tinyfpga/TinyFPGA-B-Series/bootloader/verilog/usb_fs_pe.v

module usb_fs_pe #(
  NUM_OUT_EPS = 1,
  NUM_IN_EPS = 1
) (
  input clk,
  input [6:0] dev_addr,


  ////////////////////////////////////////////////////////////////////////////////
  ////////////////////////////////////////////////////////////////////////////////
  /// USB Endpoint Interface
  ////////////////////////////////////////////////////////////////////////////////
  ////////////////////////////////////////////////////////////////////////////////

  ////////////////////
  // global endpoint interface 
  ////////////////////
  output reset,


  ////////////////////
  // out endpoint interfaces 
  ////////////////////
  input [NUM_OUT_EPS-1:0] out_ep_req,
  output [NUM_OUT_EPS-1:0] out_ep_grant,
  output [NUM_OUT_EPS-1:0] out_ep_data_avail,
  output [NUM_OUT_EPS-1:0] out_ep_setup,
  input [NUM_OUT_EPS-1:0] out_ep_data_get,
  output [7:0] out_ep_data,
  input [NUM_OUT_EPS-1:0] out_ep_stall,
  output [NUM_OUT_EPS-1:0] out_ep_acked,


  ////////////////////
  // in endpoint interfaces 
  ////////////////////
  input [NUM_IN_EPS-1:0] in_ep_req,
  output [NUM_IN_EPS-1:0] in_ep_grant,
  output [NUM_IN_EPS-1:0] in_ep_data_free,
  input [NUM_IN_EPS-1:0] in_ep_data_put,
  input [(NUM_IN_EPS*8)-1:0] in_ep_data,
  input [NUM_IN_EPS-1:0] in_ep_data_done,
  input [NUM_IN_EPS-1:0] in_ep_stall,
  output [NUM_IN_EPS-1:0] in_ep_acked,

  
  ////////////////////
  // sof interface
  ////////////////////
  output sof_valid,
  output [10:0] frame_index,



  ////////////////////////////////////////////////////////////////////////////////
  ////////////////////////////////////////////////////////////////////////////////
  /// USB TX/RX Interface
  ////////////////////////////////////////////////////////////////////////////////
  ////////////////////////////////////////////////////////////////////////////////

  inout dp,
  inout dn
);
  // in pe interface
  wire [7:0] arb_in_ep_data;

  // rx interface
  wire bit_strobe;
  wire rx_pkt_start;
  wire rx_pkt_end;
  wire [3:0] rx_pid;
  wire [6:0] rx_addr;
  wire [3:0] rx_endp;
  wire [10:0] rx_frame_num;
  wire rx_data_put;
  wire [7:0] rx_data;
  wire rx_pkt_valid;

  // tx mux
  wire in_tx_pkt_start;
  wire [3:0] in_tx_pid;
  wire out_tx_pkt_start;
  wire [3:0] out_tx_pid;
  
  // tx interface
  wire tx_pkt_start;
  wire tx_pkt_end;
  wire [3:0] tx_pid;
  wire tx_data_avail;
  wire tx_data_get;
  wire [7:0] tx_data;

  // sof interface
  assign sof_valid = rx_pkt_end && rx_pkt_valid && rx_pid == 4'b0101;
  assign frame_index = rx_frame_num;

  // d+/d- muxing and interface
  wire usb_output_enable;
  wire dp_tx;
  wire dn_tx;
  wire dp_rx;
  wire dn_rx;

  wire reset_i;
  assign reset = reset_i;


  usb_fs_in_arb #(
    .NUM_IN_EPS(NUM_IN_EPS)
  ) usb_fs_in_arb_inst (
    // endpoint interface 
    .in_ep_req(in_ep_req),
    .in_ep_grant(in_ep_grant),
    .in_ep_data(in_ep_data),

    // protocol engine interface 
    .arb_in_ep_data(arb_in_ep_data)
  );

  usb_fs_out_arb #(
    .NUM_OUT_EPS(NUM_OUT_EPS)
  ) usb_fs_out_arb_inst (
    // endpoint interface 
    .out_ep_req(out_ep_req),
    .out_ep_grant(out_ep_grant)
  );

  usb_fs_in_pe #(
    .NUM_IN_EPS(NUM_IN_EPS)
  ) usb_fs_in_pe_inst (
    .clk(clk),
    .reset(reset_i),
    .dev_addr(dev_addr),

    // endpoint interface 
    .in_ep_data_free(in_ep_data_free),
    .in_ep_data_put(in_ep_data_put),
    .in_ep_data(arb_in_ep_data),
    .in_ep_data_done(in_ep_data_done),
    .in_ep_stall(in_ep_stall),
    .in_ep_acked(in_ep_acked),

    // rx path 
    .rx_pkt_start(rx_pkt_start),
    .rx_pkt_end(rx_pkt_end),
    .rx_pkt_valid(rx_pkt_valid),
    .rx_pid(rx_pid),
    .rx_addr(rx_addr),
    .rx_endp(rx_endp),
    .rx_frame_num(rx_frame_num),

    // tx path 
    .tx_pkt_start(in_tx_pkt_start),
    .tx_pkt_end(tx_pkt_end),
    .tx_pid(in_tx_pid),
    .tx_data_avail(tx_data_avail),
    .tx_data_get(tx_data_get),
    .tx_data(tx_data)
  );

  usb_fs_out_pe #(
    .NUM_OUT_EPS(NUM_OUT_EPS)
  ) usb_fs_out_pe_inst (
    .clk(clk),
    .reset(reset_i),
    .dev_addr(dev_addr),

    // endpoint interface 
    .out_ep_data_avail(out_ep_data_avail),
    .out_ep_data_get(out_ep_data_get),
    .out_ep_data(out_ep_data),
    .out_ep_setup(out_ep_setup),
    .out_ep_stall(out_ep_stall),
    .out_ep_acked(out_ep_acked),

    // rx path 
    .rx_pkt_start(rx_pkt_start),
    .rx_pkt_end(rx_pkt_end),
    .rx_pkt_valid(rx_pkt_valid),
    .rx_pid(rx_pid),
    .rx_addr(rx_addr),
    .rx_endp(rx_endp),
    .rx_frame_num(rx_frame_num),
    .rx_data_put(rx_data_put),
    .rx_data(rx_data),

    // tx path 
    .tx_pkt_start(out_tx_pkt_start),
    .tx_pkt_end(tx_pkt_end),
    .tx_pid(out_tx_pid)
  );

  usb_fs_rx usb_fs_rx_inst (
    .clk_48mhz(clk),
    .reset(reset_i),
    .dp(dp_rx),
    .dn(dn_rx),
    .bit_strobe(bit_strobe),
    .pkt_start(rx_pkt_start),
    .pkt_end(rx_pkt_end),
    .pid(rx_pid),
    .addr(rx_addr),
    .endp(rx_endp),
    .frame_num(rx_frame_num),
    .rx_data_put(rx_data_put),
    .rx_data(rx_data),
    .valid_packet(rx_pkt_valid)
  );

  usb_fs_tx_mux usb_fs_tx_mux_inst (
    // interface to IN Protocol Engine
    .in_tx_pkt_start(in_tx_pkt_start),
    .in_tx_pid(in_tx_pid),

    // interface to OUT Protocol Engine
    .out_tx_pkt_start(out_tx_pkt_start),
    .out_tx_pid(out_tx_pid),

    // interface to tx module
    .tx_pkt_start(tx_pkt_start),
    .tx_pid(tx_pid)
  );

  usb_fs_tx usb_fs_tx_inst (
    .clk_48mhz(clk),
    .reset(reset_i),
    .bit_strobe(bit_strobe),
    .oe(usb_output_enable),
    .dp(dp_tx),
    .dn(dn_tx),
    .pkt_start(tx_pkt_start),
    .pkt_end(tx_pkt_end),
    .pid(tx_pid),
    .tx_data_avail(tx_data_avail),
    .tx_data_get(tx_data_get),
    .tx_data(tx_data)
  );

  usb_fs_mux usb_fs_mux_inst (
    .clk(clk),
    .reset(reset_i),

    // raw usb d+/d- lines
    .dp(dp),
    .dn(dn),

    // output enable
    .oe(usb_output_enable),

    // transmit value when output enabled
    .dp_tx(dp_tx),
    .dn_tx(dn_tx),

    // receive value when output disabled
    .dp_rx(dp_rx),
    .dn_rx(dn_rx)
  );
endmodule
